kreativekorp/spritelet/spritelet2_itsybitsy_m0/spritelet_font.h

#ifndef __SPRITELET_FONT__
#define __SPRITELET_FONT__

#include <Arduino.h>
#include <avr/pgmspace.h>

void tft_drawChar(int16_t x, int16_t y, unsigned char ch, uint16_t bg, uint16_t fg);
void tft_drawString(int16_t x, int16_t y, char * str, uint16_t bg, uint16_t fg);
void tft_drawStringWrapped(int16_t x, int16_t y, int16_t w, char * str, uint16_t bg, uint16_t fg);

#define BUILTIN_FONT_WIDTH    6
#define BUILTIN_FONT_HEIGHT  12
#define BUILTIN_FONT_ASCENT   9
#define BUILTIN_FONT_DESCENT  3

const uint8_t PROGMEM builtin_font[256][9] = {
  { 0x00, 0x00, 0x00, 0x00, 0x00, 0x00, 0x00, 0x00, 0x00 }, /* null */
  { 0x00, 0x04, 0x08, 0x00, 0x00, 0x00, 0x00, 0x00, 0x00 }, /* grave */
  { 0x00, 0x02, 0x94, 0x00, 0x00, 0x00, 0x00, 0x00, 0x00 }, /* dbl acute */
  { 0x00, 0x02, 0x00, 0x00, 0x00, 0x00, 0x00, 0x00, 0x00 }, /* dot */
  { 0x00, 0x85, 0x08, 0x00, 0x00, 0x00, 0x00, 0x00, 0x00 }, /* ring */
  { 0x00, 0x05, 0x08, 0x00, 0x00, 0x00, 0x00, 0x00, 0x00 }, /* caron */
  { 0x00, 0x08, 0x9C, 0x00, 0x00, 0x00, 0x00, 0x00, 0x00 }, /* breve */
  { 0x00, 0x00, 0x00, 0x00, 0x00, 0x00, 0x00, 0x84, 0x0C }, /* ogonek */
  { 0x00, 0x00, 0x0F, 0x46, 0x54, 0x4F, 0x00, 0x00, 0x00 }, /* bksp */
  { 0x00, 0x00, 0x12, 0x2B, 0xE2, 0x92, 0x00, 0x00, 0x00 }, /* tab */
  { 0x00, 0x00, 0x36, 0x00, 0x85, 0x22, 0x00, 0x00, 0x00 }, /* enter */
  { 0x00, 0x00, 0x36, 0x40, 0x81, 0x06, 0x00, 0x00, 0x00 }, /* alt */
  { 0x00, 0x02, 0x14, 0x8B, 0x65, 0x14, 0x70, 0x00, 0x00 }, /* shift */
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
  { 0x00, 0x05, 0x00, 0x8A, 0x28, 0xA6, 0x68, 0x00, 0x00 }, /* u" */
  { 0x00, 0x42, 0x00, 0x8A, 0x28, 0xA6, 0x68, 0x27, 0x00 }, /* y' */
  { 0x00, 0x08, 0x20, 0xB3, 0x28, 0xA2, 0xF2, 0x08, 0x00 }, /* thorn */
  { 0x00, 0x05, 0x00, 0x8A, 0x28, 0xA6, 0x68, 0x27, 0x00 }, /* y" */
};

const uint8_t PROGMEM word_wrap_data[64] = {
  0xC0, 0x00, 0xFF, 0xF0, /* null - fl */
  0x00, 0x00, 0x03, 0x00, /* KK - approx */
  0xD0, 0xA0, 0x92, 0x11, /* space - / */
  0x00, 0x00, 0x00, 0x01, /* 0 - ? */
  0x00, 0x00, 0x00, 0x00, /* @ - O */
  0x00, 0x00, 0x02, 0x90, /* P - _ */
  0x00, 0x00, 0x00, 0x00, /* ` - o */
  0x00, 0x00, 0x02, 0x53, /* p - cursor */
  0x88, 0x90, 0x20, 0x00, /* euro - dotless i */
  0x00, 0x05, 0x00, 0x00, /* meta - Y" */
  0x2A, 0xA0, 0x00, 0x10, /* nbsp - macron */
  0xA0, 0x80, 0x00, 0x02, /* degree - inv ? */
  0x00, 0x00, 0x00, 0x00, /* A` - I" */
  0x00, 0x00, 0x00, 0x00, /* Eth - sz */
  0x00, 0x00, 0x00, 0x00, /* a` - i" */
  0x00, 0x00, 0x00, 0x00, /* eth - y" */
};

#endif
