kreativekorp/spritelet/spritelet2_itsybitsy_m0/toasters.cpp

#include <Arduino.h>
#include <avr/pgmspace.h>
#include "spi.h"
#include "spritelet_input.h"
#include "st7735_pins.h"
#include "st7735.h"
#include "toasters.h"

extern ST7735 tft;

#define N_FLYERS 5

static struct Flyer {
  int16_t x;
  int16_t y;
  int8_t  depth;
  uint8_t frame;
} flyer[N_FLYERS];

static const uint8_t PROGMEM toaster_mask_0[] = {
  0x00, 0x00, 0x00, 0x00, 0x00, 0x10, 0x00, 0x00,
  0x00, 0x20, 0x00, 0x00, 0x00, 0x88, 0x00, 0x00,
  0x00, 0x10, 0x00, 0x00, 0x00, 0x43, 0xF8, 0x00,
  0x00, 0x1F, 0x80, 0x00, 0x00, 0x7C, 0x3F, 0x80,
  0x01, 0xF1, 0xF8, 0xF0, 0x07, 0xC7, 0xC7, 0x00,
  0x0F, 0x1F, 0x08, 0x2B, 0x1E, 0x7C, 0x11, 0x00,
  0x04, 0xF0, 0x20, 0x56, 0x61, 0xE4, 0x22, 0x00,
  0x78, 0x48, 0x40, 0xA8, 0x4E, 0x10, 0x44, 0x00,
  0x53, 0x90, 0x81, 0xF8, 0x5C, 0xA0, 0x90, 0x58,
  0x7C, 0xA1, 0x07, 0x90, 0x74, 0xA1, 0x21, 0x38,
  0x7F, 0xB5, 0x0E, 0x30, 0x77, 0xB0, 0x90, 0x78,
  0x7F, 0xB4, 0x60, 0xF0, 0x77, 0xBB, 0x03, 0xE0,
  0x7F, 0xBC, 0x0F, 0xC0, 0x77, 0xBF, 0xFF, 0x00,
  0x7F, 0xBF, 0xFC, 0x00, 0x3F, 0xBF, 0xF0, 0x00,
  0x1F, 0xBF, 0xC0, 0x00, 0x07, 0xBE, 0x00, 0x00,
  0x01, 0xB0, 0x00, 0x00, 0x00, 0x00, 0x00, 0x00
};

static const uint8_t PROGMEM toaster_mask_1[] = {
  0x00, 0x00, 0x00, 0x00, 0x00, 0x00, 0x00, 0x00,
  0x00, 0x00, 0x00, 0x00, 0x00, 0x00, 0x00, 0x00,
  0x00, 0x00, 0x00, 0x00, 0x00, 0x43, 0xF8, 0x00,
  0x00, 0x1F, 0x80, 0x00, 0x00, 0x7C, 0x3F, 0x80,
  0x01, 0xF1, 0xF8, 0x00, 0x07, 0xC7, 0xC1, 0xE0,
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
    flyer[i].depth = random(16) + 10;
    flyer[i].frame = random(4) ? random(4) : 4;
  }
  return 1;
}

uint8_t toasters_loop(void) {
  uint32_t t = millis();
  uint8_t line[128];
  uint8_t y, x, i, f;
  int16_t fy, fx;
  uint8_t * mask;
  uint8_t * bitmap;
  uint8_t mbi, mbm;

  tft.setAddrWindow(0, 0, 127, 127);
  digitalWrite(TFT_DC, HIGH);
  digitalWrite(TFT_CS, LOW );
  for (y = 0; y < 128; y++) {
    for (x = 0; x < 128; x++) {
      line[x] = 0;
    }
    for (i = 0; i < N_FLYERS; i++) {
      fy = flyer[i].y >> 4;
      if ((y >= fy) && (y < fy + 32)) {
        f = flyer[i].frame;
        mask = (uint8_t *)pgm_read_dword(&toaster_mask[f]);
        bitmap = (uint8_t *)pgm_read_dword(&toaster_bitmap[f]);
        mbi = ((y - fy) << 2);
        mbm = 0x80;
        for (fx = flyer[i].x >> 4, x = 0; x < 32; x++, fx++) {
          if (fx >= 0 && fx < 128) {
            if (pgm_read_byte(&mask[mbi]) & mbm) line[fx] = 0;
            if (pgm_read_byte(&bitmap[mbi]) & mbm) line[fx] = -1;
          }
          mbm >>= 1;
          if (!mbm) {
            mbm = 0x80;
            mbi++;
          }
        }
      }
    }
    for (x = 0; x < 128; x++) {
      SPI_write(line[x]);
      SPI_write(line[x]);
    }
  }
  digitalWrite(TFT_CS, HIGH);

  for (i = 0; i < N_FLYERS; i++) {
    if (flyer[i].frame < 4) flyer[i].frame = ((flyer[i].frame + 1) & 3);
    flyer[i].x -= flyer[i].depth;
    flyer[i].x -= flyer[i].depth;
    flyer[i].y += flyer[i].depth;
    if ((flyer[i].y >= 2048) || (flyer[i].x <= -512)) {
      if (random(2)) {
        flyer[i].x = random(128) << 4;
        flyer[i].y = -512;
      } else {
        flyer[i].x = 2048;
        flyer[i].y = (random(160) - 32) << 4;
      }
      flyer[i].depth = random(16) + 10;
      flyer[i].frame = random(4) ? random(4) : 4;
    }
  }

  do { 
    if (input_get() == INPUT_CTR) {
      tft.fillScreen(0);
      delay(50);
      while (input_get());
      delay(50);
      return 0;
    }
  } while (millis() - t < 30);
  return 1;
}
