kreativekorp/spritelet/spritelet2_itsybitsy_m0/spritelet_pins.h

#ifndef __SPRITELET_PINS__
#define __SPRITELET_PINS__

#include <Arduino.h>

#define VS_GND   5
#define VS_POS   7
#define JOY_COM  A0
#define JOY_CTR  A1
#define JOY_UP   A2
#define JOY_DN   A3
#define JOY_LT   A4
#define JOY_RT   A5

#endif
