kreativekorp/spritelet/spritelet2_itsybitsy_m0/picofs_pins.h

/**********************************************************
 * PicoFS FAT Library for Arduino by Rebecca Bettencourt. *
 * Based on PetitFS by ChaN. MIT license.                 *
 **********************************************************/

#ifndef __PICOFS_PINS__
#define __PICOFS_PINS__

#include <Arduino.h>

// Chip select line for SD card.
#define SD_CS  12

#endif
