kreativekorp/spritelet/spritelet2_itsybitsy_m0/st7735_commands.h

/**************************************************************************/
/* ST7735 Driver Library for Adafruit 1.44" TFT Breakout with SD Card.    */
/* Based on Adafruit_ST7735_Library but stripped down and with bug fixes. */
/* Written by Rebecca Bettencourt. MIT license.                           */
/**************************************************************************/

#ifndef __ST7735_COMMANDS__
#define __ST7735_COMMANDS__

#define ST7735_NOP     0x00
#define ST7735_SWRESET 0x01
#define ST7735_RDDID   0x04
#define ST7735_RDDST   0x09

#define ST7735_SLPIN   0x10
#define ST7735_SLPOUT  0x11
#define ST7735_PTLON   0x12
#define ST7735_NORON   0x13

#define ST7735_INVOFF  0x20
#define ST7735_INVON   0x21
#define ST7735_DISPOFF 0x28
#define ST7735_DISPON  0x29
#define ST7735_CASET   0x2A
#define ST7735_RASET   0x2B
#define ST7735_RAMWR   0x2C
#define ST7735_RAMRD   0x2E

#define ST7735_PTLAR   0x30
#define ST7735_MADCTL  0x36
#define ST7735_COLMOD  0x3A

#define ST7735_FRMCTR1 0xB1
#define ST7735_FRMCTR2 0xB2
#define ST7735_FRMCTR3 0xB3
#define ST7735_INVCTR  0xB4
#define ST7735_DISSET5 0xB6

#define ST7735_PWCTR1  0xC0
#define ST7735_PWCTR2  0xC1
#define ST7735_PWCTR3  0xC2
#define ST7735_PWCTR4  0xC3
#define ST7735_PWCTR5  0xC4
#define ST7735_VMCTR1  0xC5

#define ST7735_RDID1   0xDA
#define ST7735_RDID2   0xDB
#define ST7735_RDID3   0xDC
#define ST7735_RDID4   0xDD

#define ST7735_GMCTRP1 0xE0
#define ST7735_GMCTRN1 0xE1

#define ST7735_PWCTR6  0xFC

#define ST7735_DELAY   0xFE
#define ST7735_EOF     0xFF

#define ST7735_BLACK   0x0000
#define ST7735_RED     0xF800
#define ST7735_GREEN   0x07E0
#define ST7735_BLUE    0x001F
#define ST7735_CYAN    0x07FF
#define ST7735_MAGENTA 0xF81F
#define ST7735_YELLOW  0xFFE0
#define ST7735_WHITE   0xFFFF

#define MADCTL_MY      0x80
#define MADCTL_MX      0x40
#define MADCTL_MV      0x20
#define MADCTL_ML      0x10
#define MADCTL_MH      0x04
#define MADCTL_BGR     0x08
#define MADCTL_RGB     0x00

#endif
